tataranovich/magnetic-loop-antenna/freecad/circle.FCStd

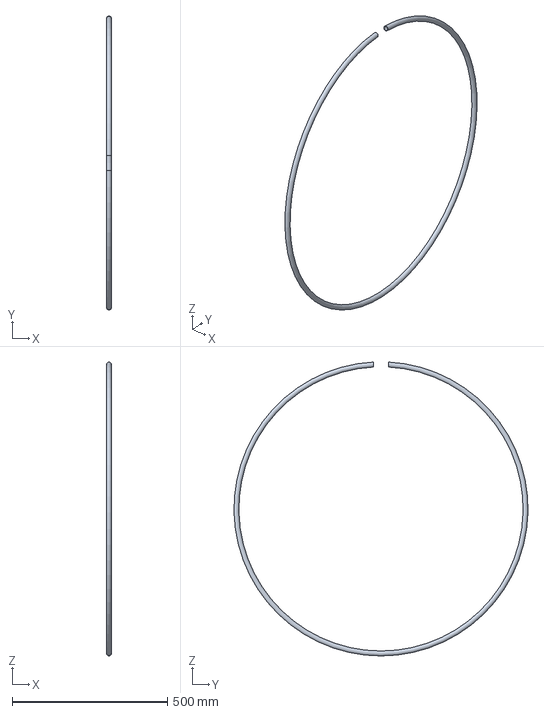
[picture p18: CAD file, 2026-03-06]
freecad/circle.FCStd
16.0 x 945.7 x 945.3 mm
