tataranovich/magnetic-loop-antenna/freecad/end.FCStd

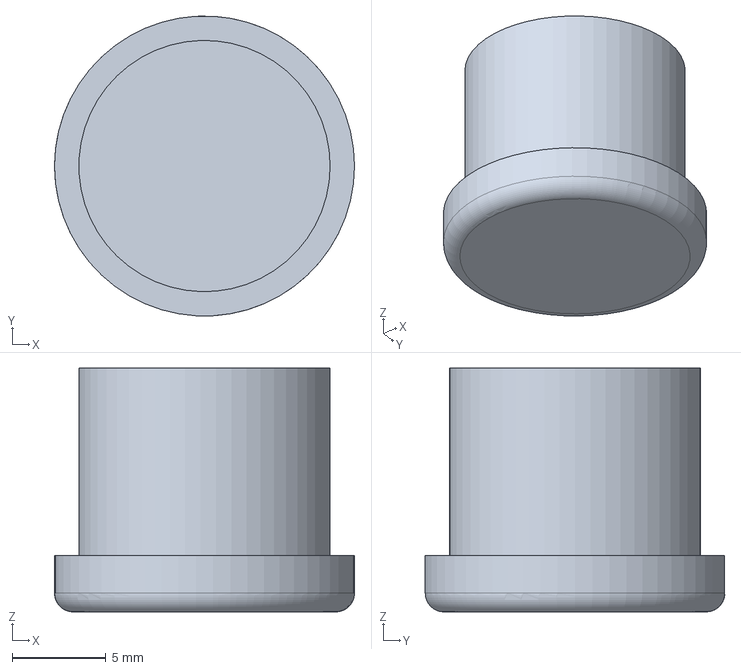
[picture p19: CAD file, 2026-03-06]
freecad/end.FCStd
16.0 x 16.0 x 13.0 mm
