tataranovich/magnetic-loop-antenna/freecad/circle2.FCStd

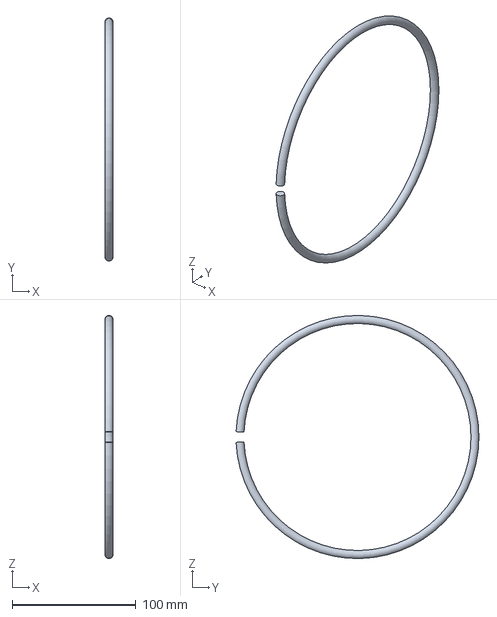
[picture p20: CAD file, 2026-03-06]
freecad/circle2.FCStd
6.49 x 196.4 x 196.5 mm
